dqydj/VGAtonic/Hardware_Rev_B/Widescreen Version Firmware/AVR_ATTiny2313a_revB_848480_Firmware/uart.ino

/*****************************************

            UART Transfers
  
******************************************/

/*
 * Receive a character from UART
 */
unsigned char inline uart_receive (void)
{
    while( (UCSRA) & (1<<RXC) == 0 );                  
    return UDR;                                   
}

/*
 * Send a character over UART
 */
void inline uart_transmit (unsigned char data)
{
    while ( ( UCSRA & (1<<UDRE)) == 0 );                // wait while register is free
    UDR = data;                                   // load data in the register
}

/*
 * Send a string over UART
 */
void uart_puts(const char *s )
{
    while (*s) 
      uart_transmit (*s++);

}


/*****************************************

            UART Setup
  
******************************************/

/* Turn on the Hardware UART Credit abcminiuser @ http://www.avrfreaks.net/forum/tut-soft-using-usart-interrupt-driven-serial-comms */
void inline setup_uart() 
{
  uart_speed_9600();
  UCSRB = (1 << RXEN) | (1 << TXEN) | (1 << RXCIE);
  UCSRC = (1 << USBS) | (3 << UCSZ0);
  sei();
}

void inline uart_speed_300() {
  UBRRH = (uint8_t)(BAUD_PRESCALE(300) >> 8); 
  UBRRL = (uint8_t)(BAUD_PRESCALE(300)); 
}

void inline uart_speed_2400() {
  UBRRH = (uint8_t)(BAUD_PRESCALE(2400) >> 8); 
  UBRRL = (uint8_t)(BAUD_PRESCALE(2400)); 
}

void inline uart_speed_9600() {
  UBRRH = (uint8_t)(BAUD_PRESCALE(9600) >> 8); 
  UBRRL = (uint8_t)(BAUD_PRESCALE(9600)); 
}

void inline uart_speed_38400() {
  UBRRH = (uint8_t)(BAUD_PRESCALE(38400) >> 8); 
  UBRRL = (uint8_t)(BAUD_PRESCALE(38400)); 
}

void inline uart_speed_57600() {
  UBRRH = (uint8_t)(BAUD_PRESCALE_U2X(57600) >> 8); 
  UBRRL = (uint8_t)(BAUD_PRESCALE_U2X(57600)); 
}

void inline uart_speed_115200() {
  UBRRH = (uint8_t)(BAUD_PRESCALE(115200) >> 8); 
  UBRRL = (uint8_t)(BAUD_PRESCALE(115200)); 
}


/*****************************************

            Interrupt Handlers
  
******************************************/

/*
 * For speed reasons, only write into our ring buffer and get out.  Deal with it elsewhere.
 */
ISR(USART_RX_vect) 
{
  uint8_t tmp = UDR;
  if (rxn==BUFFER_SIZE)
    rxn=0;
  RX_BUFF[rxn++] = tmp;  
  rx_flag=1;
}
